wt29/HWSRedirector/kicad/HWSRedirector.kicad_sch

## KiCad design kicad/HWSRedirector.kicad_sch (2025-01-24, an earlier design)

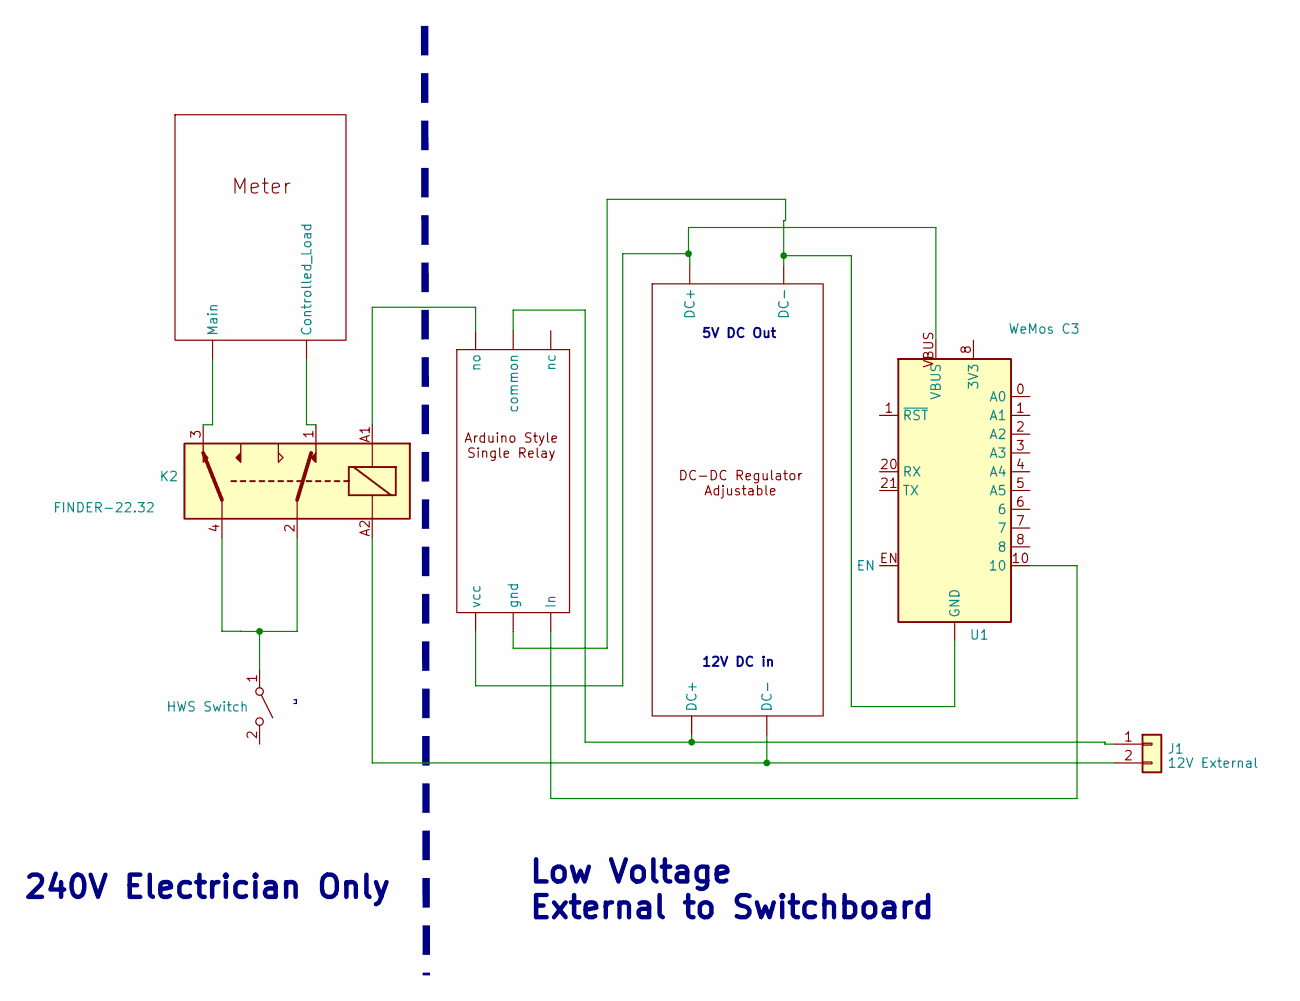
[picture p4: schematic HWSRedirector.kicad_sch]

Parts:
J1: 12V External
K2: FINDER-22.32; Relay_DPDT_Finder_30.22
R1: (no value)
Reg2: (no value)
SW1: HWS Switch
U1: WeMos C3; WEMOS_C3_mini_light
U2: (no value)

Connections:
unnamed: J1.1, R1., Reg2.
unnamed: J1.2, K2.A2, Reg2.
unnamed: K2.1, U2.
unnamed: K2.2, K2.4, SW1.1 (A)
unnamed: K2.3, U2.
unnamed: K2.A1, R1.
unnamed: R1., Reg2., U1. (GND), U1.10, U1.VBUS

Notes on the sheet:
5V DC Out
Low Voltage External to Switchboard
12V DC in
240V Electrician Only
